e-labInnovations/CampusCast/main/src/WiFiManager/wm_strings_en.h

/**
 * wm_strings_en.h
 * engligh strings for
 * WiFiManager, a library for the ESP8266/Arduino platform
 * for configuration of WiFi credentials using a Captive Portal
 *
 * @author Creator tzapu
 * @author tablatronix
 * @version 0.0.0
 * @license MIT
 */

#ifndef _WM_STRINGS_EN_H_
#define _WM_STRINGS_EN_H_


#ifndef WIFI_MANAGER_OVERRIDE_STRINGS
// !!! ABOVE WILL NOT WORK if you define in your sketch, must be build flag, if anyone one knows how to order includes to be able to do this it would be neat.. I have seen it done..

// strings files must include a consts file!
#include "wm_consts_en.h" // include constants, tokens, routes

const char WM_LANGUAGE[] PROGMEM = "en-US"; // i18n lang code

const char HTTP_HEAD_START[]       PROGMEM = "<!DOCTYPE html>"
"<html lang='en'><head>"
"<meta name='format-detection' content='telephone=no'>"
"<meta charset='UTF-8'>"
"<meta  name='viewport' content='width=device-width,initial-scale=1,user-scalable=no'/>"
"<title>{v}</title>";

const char HTTP_SCRIPT[]           PROGMEM = "<script>function c(l){"
"document.getElementById('s').value=l.getAttribute('data-ssid')||l.innerText||l.textContent;"
"p = l.nextElementSibling.classList.contains('l');"
"document.getElementById('p').disabled = !p;"
"if(p)document.getElementById('p').focus();};"
"function f() {var x = document.getElementById('p');x.type==='password'?x.type='text':x.type='password';}"
"</script>"; // @todo add button states, disable on click , show ack , spinner etc

const char HTTP_HEAD_END[]         PROGMEM = "</head><body class='{c}'><div class='wrap'>"; // {c} = _bodyclass
// example of embedded logo, base64 encoded inline, No styling here
const char HTTP_ROOT_MAIN[]        PROGMEM = "<svg id=\"OBJECTS\" xmlns=\"http://www.w3.org/2000/svg\" viewBox=\"0 0 600 100\"><defs><style>.cls-3{fill:#3cb371}</style></defs><text transform=\"translate(32.22 76.61)\" style=\"font-size:81px\"><tspan x=\"0\" y=\"0\" style=\"font-family:MontserratAlternates-Bold,'Montserrat Alternates';font-weight:700;letter-spacing:-.02em;fill:#2b2f60\">C</tspan><tspan x=\"57.83\" y=\"0\" style=\"font-family:MontserratAlternates-Bold,'Montserrat Alternates';font-weight:700;fill:#2b2f60\">ampus</tspan><tspan x=\"353.24\" y=\"0\" style=\"letter-spacing:-.02em;fill:#3cb371;font-family:MontserratAlternates-Regular,'Montserrat Alternates'\">C</tspan><tspan x=\"409.61\" y=\"0\" style=\"fill:#3cb371;font-family:MontserratAlternates-Regular,'Montserrat Alternates'\">ast</tspan></text><path d=\"m42.29 60.68-6.91 17.67c-1.11 2.84 1.86 5.56 4.59 4.2l19.38-9.64-17.06-12.23Z\" style=\"fill:#2b2f60\"/><rect class=\"cls-3\" x=\"438.47\" y=\"11.64\" width=\"15.39\" height=\"3.88\" rx=\"1.94\" ry=\"1.94\" transform=\"rotate(-49.2 446.163 13.581)\"/><rect class=\"cls-3\" x=\"423.93\" y=\"7.52\" width=\"15.39\" height=\"3.88\" rx=\"1.94\" ry=\"1.94\" transform=\"rotate(-99.2 431.624 9.465)\"/><rect class=\"cls-3\" x=\"444.66\" y=\"25.41\" width=\"15.39\" height=\"3.88\" rx=\"1.94\" ry=\"1.94\" transform=\"rotate(.8 452.844 27.636)\"/></svg><h3>{v}</h3>";
// const char HTTP_ROOT_MAIN[]        PROGMEM = "<h1>{t}</h1><h3>{v}</h3>";

const char * const HTTP_PORTAL_MENU[] PROGMEM = {
"<form action='/wifi'    method='get'><button>Configure WiFi</button></form><br/>\n", // MENU_WIFI
"<form action='/0wifi'   method='get'><button>Configure WiFi (No Scan)</button></form><br/>\n", // MENU_WIFINOSCAN
"<form action='/info'    method='get'><button>Info</button></form><br/>\n", // MENU_INFO
"<form action='/param'   method='get'><button>Setup</button></form><br/>\n",//MENU_PARAM
"<form action='/close'   method='get'><button>Close</button></form><br/>\n", // MENU_CLOSE
"<form action='/restart' method='get'><button>Restart</button></form><br/>\n",// MENU_RESTART
"<form action='/exit'    method='get'><button>Exit</button></form><br/>\n",  // MENU_EXIT
"<form action='/erase'   method='get'><button class='D'>Erase</button></form><br/>\n", // MENU_ERASE
"<form action='/update'  method='get'><button>Update</button></form><br/>\n",// MENU_UPDATE
"<hr><br/>" // MENU_SEP
};

// const char HTTP_PORTAL_OPTIONS[]   PROGMEM = strcat(HTTP_PORTAL_MENU[0] , HTTP_PORTAL_MENU[3] , HTTP_PORTAL_MENU[7]);
const char HTTP_PORTAL_OPTIONS[]   PROGMEM = "";
const char HTTP_ITEM_QI[]          PROGMEM = "<div role='img' aria-label='{r}%' title='{r}%' class='q q-{q} {i} {h}'></div>"; // rssi icons
const char HTTP_ITEM_QP[]          PROGMEM = "<div class='q {h}'>{r}%</div>"; // rssi percentage {h} = hidden showperc pref
const char HTTP_ITEM[]             PROGMEM = "<div><a href='#p' onclick='c(this)' data-ssid='{V}'>{v}</a>{qi}{qp}</div>"; // {q} = HTTP_ITEM_QI, {r} = HTTP_ITEM_QP
// const char HTTP_ITEM[]            PROGMEM = "<div><a href='#p' onclick='c(this)'>{v}</a> {R} {r}% {q} {e}</div>"; // test all tokens

const char HTTP_FORM_START[]       PROGMEM = "<form method='POST' action='{v}'>";
const char HTTP_FORM_WIFI[]        PROGMEM = "<label for='s'>SSID</label><input id='s' name='s' maxlength='32' autocorrect='off' autocapitalize='none' placeholder='{v}'><br/><label for='p'>Password</label><input id='p' name='p' maxlength='64' type='password' placeholder='{p}'><input type='checkbox' onclick='f()'> Show Password";
const char HTTP_FORM_WIFI_END[]    PROGMEM = "";
const char HTTP_FORM_STATIC_HEAD[] PROGMEM = "<hr><br/>";
const char HTTP_FORM_END[]         PROGMEM = "<br/><br/><button type='submit'>Save</button></form>";
const char HTTP_FORM_LABEL[]       PROGMEM = "<label for='{i}'>{t}</label>";
const char HTTP_FORM_PARAM_HEAD[]  PROGMEM = "<hr><br/>";
const char HTTP_FORM_PARAM[]       PROGMEM = "<br/><input id='{i}' name='{n}' maxlength='{l}' value='{v}' {c}>\n"; // do not remove newline!

const char HTTP_SCAN_LINK[]        PROGMEM = "<br/><form action='/wifi?refresh=1' method='POST'><button name='refresh' value='1'>Refresh</button></form>";
const char HTTP_SAVED[]            PROGMEM = "<div class='msg'>Saving Credentials<br/>Trying to connect ESP to network.<br />If it fails reconnect to AP to try again</div>";
const char HTTP_PARAMSAVED[]       PROGMEM = "<div class='msg S'>Saved<br/></div>";
const char HTTP_END[]              PROGMEM = "</div></body></html>";
const char HTTP_ERASEBTN[]         PROGMEM = "<br/><form action='/erase' method='get'><button class='D'>Erase WiFi Config</button></form>";
const char HTTP_UPDATEBTN[]        PROGMEM = "<br/><form action='/update' method='get'><button>Update</button></form>";
const char HTTP_BACKBTN[]          PROGMEM = "<hr><br/><form action='/' method='get'><button>Back</button></form>";

const char HTTP_STATUS_ON[]        PROGMEM = "<div class='msg S'><strong>Connected</strong> to {v}<br/><em><small>with IP {i}</small></em></div>";
const char HTTP_STATUS_OFF[]       PROGMEM = "<div class='msg {c}'><strong>Not Connected</strong> to {v}{r}</div>"; // {c=class} {v=ssid} {r=status_off}
const char HTTP_STATUS_OFFPW[]     PROGMEM = "<br/>Authentication Failure"; // STATION_WRONG_PASSWORD,  no eps32
const char HTTP_STATUS_OFFNOAP[]   PROGMEM = "<br/>AP not found";   // WL_NO_SSID_AVAIL
const char HTTP_STATUS_OFFFAIL[]   PROGMEM = "<br/>Could not Connect"; // WL_CONNECT_FAILED
const char HTTP_STATUS_NONE[]      PROGMEM = "<div class='msg'>No AP set</div>";
const char HTTP_BR[]               PROGMEM = "<br/>";

const char HTTP_STYLE[]            PROGMEM = "<style>"
".c,body{text-align:center;font-family:verdana}div,input,select{padding:5px;font-size:1em;margin:5px 0;box-sizing:border-box}"
"input,button,select,.msg{border-radius:.3rem;width: 100%}input[type=radio],input[type=checkbox]{width:auto}"
"button,input[type='button'],input[type='submit']{cursor:pointer;border:0;background-color:#1fa3ec;color:#fff;line-height:2.4rem;font-size:1.2rem;width:100%}"
"input[type='file']{border:1px solid #1fa3ec}"
".wrap {text-align:left;display:inline-block;min-width:260px;max-width:500px}"
// links
"a{color:#000;font-weight:700;text-decoration:none}a:hover{color:#1fa3ec;text-decoration:underline}"
// quality icons
".q{height:16px;margin:0;padding:0 5px;text-align:right;min-width:38px;float:right}.q.q-0:after{background-position-x:0}.q.q-1:after{background-position-x:-16px}.q.q-2:after{background-position-x:-32px}.q.q-3:after{background-position-x:-48px}.q.q-4:after{background-position-x:-64px}.q.l:before{background-position-x:-80px;padding-right:5px}.ql .q{float:left}.q:after,.q:before{content:'';width:16px;height:16px;display:inline-block;background-repeat:no-repeat;background-position: 16px 0;"
"background-image:url('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');}"
// icons @2x media query (32px rescaled)
"@media (-webkit-min-device-pixel-ratio: 2),(min-resolution: 192dpi){.q:before,.q:after {"
"background-image:url('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');"
"background-size: 95px 16px;}}"
// msg callouts
".msg{padding:20px;margin:20px 0;border:1px solid #eee;border-left-width:5px;border-left-color:#777}.msg h4{margin-top:0;margin-bottom:5px}.msg.P{border-left-color:#1fa3ec}.msg.P h4{color:#1fa3ec}.msg.D{border-left-color:#dc3630}.msg.D h4{color:#dc3630}.msg.S{border-left-color: #5cb85c}.msg.S h4{color: #5cb85c}"
// lists
"dt{font-weight:bold}dd{margin:0;padding:0 0 0.5em 0;min-height:12px}"
"td{vertical-align: top;}"
".h{display:none}"
"button{transition: 0s opacity;transition-delay: 3s;transition-duration: 0s;cursor: pointer}"
"button.D{background-color:#dc3630}"
"button:active{opacity:50% !important;cursor:wait;transition-delay: 0s}"
// invert
"body.invert,body.invert a,body.invert h1 {background-color:#060606;color:#fff;}"
"body.invert .msg{color:#fff;background-color:#282828;border-top:1px solid #555;border-right:1px solid #555;border-bottom:1px solid #555;}"
"body.invert .q[role=img]{-webkit-filter:invert(1);filter:invert(1);}"
":disabled {opacity: 0.5;}"
"</style>";

#ifndef WM_NOHELP
const char HTTP_HELP[]             PROGMEM =
 "<br/><h3>Available Pages</h3><hr>"
 "<table class='table'>"
 "<thead><tr><th>Page</th><th>Function</th></tr></thead><tbody>"
 "<tr><td><a href='/'>/</a></td>"
 "<td>Menu page.</td></tr>"
 "<tr><td><a href='/wifi'>/wifi</a></td>"
 "<td>Show WiFi scan results and enter WiFi configuration.(/0wifi noscan)</td></tr>"
 "<tr><td><a href='/wifisave'>/wifisave</a></td>"
 "<td>Save WiFi configuration information and configure device. Needs variables supplied.</td></tr>"
 "<tr><td><a href='/param'>/param</a></td>"
 "<td>Parameter page</td></tr>"
 "<tr><td><a href='/info'>/info</a></td>"
 "<td>Information page</td></tr>"
 "<tr><td><a href='/u'>/u</a></td>"
 "<td>OTA Update</td></tr>"
 "<tr><td><a href='/close'>/close</a></td>"
 "<td>Close the captiveportal popup,configportal will remain active</td></tr>"
 "<tr><td>/exit</td>"
 "<td>Exit Config Portal, configportal will close</td></tr>"
 "<tr><td>/restart</td>"
 "<td>Reboot the device</td></tr>"
 "<tr><td>/erase</td>"
 "<td>Erase WiFi configuration and reboot Device. Device will not reconnect to a network until new WiFi configuration data is entered.</td></tr>"
 "</table>";
#else
const char HTTP_HELP[]             PROGMEM = "";
#endif

const char HTTP_UPDATE[] PROGMEM = "Upload New Firmware<br/><form method='POST' action='u' enctype='multipart/form-data' onchange=\"(function(el){document.getElementById('uploadbin').style.display = el.value=='' ? 'none' : 'initial';})(this)\"><input type='file' name='update' accept='.bin,application/octet-stream'><button id='uploadbin' type='submit' class='h D'>Update</button></form><small><a href='http://192.168.4.1/update' target='_blank'>* May not function inside captive portal, Open in browser http://192.168.4.1</a><small>";
const char HTTP_UPDATE_FAIL[] PROGMEM = "<div class='msg D'><strong>Update Failed!</strong><Br/>Reboot device and try again</div>";
const char HTTP_UPDATE_SUCCESS[] PROGMEM = "<div class='msg S'><strong>Update Successful.  </strong> <br/> Device Rebooting now...</div>";

#ifdef WM_JSTEST
const char HTTP_JS[] PROGMEM =
"<script>function postAjax(url, data, success) {"
"    var params = typeof data == 'string' ? data : Object.keys(data).map("
"            function(k){ return encodeURIComponent(k) + '=' + encodeURIComponent(data[k]) }"
"        ).join('&');"
"    var xhr = window.XMLHttpRequest ? new XMLHttpRequest() : new ActiveXObject(\"Microsoft.XMLHTTP\");"
"    xhr.open('POST', url);"
"    xhr.onreadystatechange = function() {"
"        if (xhr.readyState>3 && xhr.status==200) { success(xhr.responseText); }"
"    };"
"    xhr.setRequestHeader('X-Requested-With', 'XMLHttpRequest');"
"    xhr.setRequestHeader('Content-Type', 'application/x-www-form-urlencoded');"
"    xhr.send(params);"
"    return xhr;}"
"postAjax('/status', 'p1=1&p2=Hello+World', function(data){ console.log(data); });"
"postAjax('/status', { p1: 1, p2: 'Hello World' }, function(data){ console.log(data); });"
"</script>";
#endif

// Info html
// @todo remove html elements from progmem, repetetive strings
#ifdef ESP32
	const char HTTP_INFO_esphead[]    PROGMEM = "<h3>esp32</h3><hr><dl>";
	const char HTTP_INFO_chiprev[]    PROGMEM = "<dt>Chip Rev</dt><dd>{1}</dd>";
  	const char HTTP_INFO_lastreset[]  PROGMEM = "<dt>Last reset reason</dt><dd>CPU0: {1}<br/>CPU1: {2}</dd>";
  	const char HTTP_INFO_aphost[]     PROGMEM = "<dt>Access Point Hostname</dt><dd>{1}</dd>";
    const char HTTP_INFO_psrsize[]    PROGMEM = "<dt>PSRAM Size</dt><dd>{1} bytes</dd>";
	const char HTTP_INFO_temp[]       PROGMEM = "<dt>Temperature</dt><dd>{1} C&deg; / {2} F&deg;</dd><dt>Hall</dt><dd>{3}</dd>";
#else
	const char HTTP_INFO_esphead[]    PROGMEM = "<h3>esp8266</h3><hr><dl>";
	const char HTTP_INFO_fchipid[]    PROGMEM = "<dt>Flash Chip ID</dt><dd>{1}</dd>";
	const char HTTP_INFO_corever[]    PROGMEM = "<dt>Core Version</dt><dd>{1}</dd>";
	const char HTTP_INFO_bootver[]    PROGMEM = "<dt>Boot Version</dt><dd>{1}</dd>";
	const char HTTP_INFO_lastreset[]  PROGMEM = "<dt>Last reset reason</dt><dd>{1}</dd>";
	const char HTTP_INFO_flashsize[]  PROGMEM = "<dt>Real Flash Size</dt><dd>{1} bytes</dd>";
#endif

const char HTTP_INFO_memsmeter[]  PROGMEM = "<br/><progress value='{1}' max='{2}'></progress></dd>";
const char HTTP_INFO_memsketch[]  PROGMEM = "<dt>Memory - Sketch Size</dt><dd>Used / Total bytes<br/>{1} / {2}";
const char HTTP_INFO_freeheap[]   PROGMEM = "<dt>Memory - Free Heap</dt><dd>{1} bytes available</dd>";
const char HTTP_INFO_wifihead[]   PROGMEM = "<br/><h3>WiFi</h3><hr>";
const char HTTP_INFO_uptime[]     PROGMEM = "<dt>Uptime</dt><dd>{1} Mins {2} Secs</dd>";
const char HTTP_INFO_chipid[]     PROGMEM = "<dt>Chip ID</dt><dd>{1}</dd>";
const char HTTP_INFO_idesize[]    PROGMEM = "<dt>Flash Size</dt><dd>{1} bytes</dd>";
const char HTTP_INFO_sdkver[]     PROGMEM = "<dt>SDK Version</dt><dd>{1}</dd>";
const char HTTP_INFO_cpufreq[]    PROGMEM = "<dt>CPU Frequency</dt><dd>{1}MHz</dd>";
const char HTTP_INFO_apip[]       PROGMEM = "<dt>Access Point IP</dt><dd>{1}</dd>";
const char HTTP_INFO_apmac[]      PROGMEM = "<dt>Access Point MAC</dt><dd>{1}</dd>";
const char HTTP_INFO_apssid[]     PROGMEM = "<dt>Access Point SSID</dt><dd>{1}</dd>";
const char HTTP_INFO_apbssid[]    PROGMEM = "<dt>BSSID</dt><dd>{1}</dd>";
const char HTTP_INFO_stassid[]    PROGMEM = "<dt>Station SSID</dt><dd>{1}</dd>";
const char HTTP_INFO_staip[]      PROGMEM = "<dt>Station IP</dt><dd>{1}</dd>";
const char HTTP_INFO_stagw[]      PROGMEM = "<dt>Station Gateway</dt><dd>{1}</dd>";
const char HTTP_INFO_stasub[]     PROGMEM = "<dt>Station Subnet</dt><dd>{1}</dd>";
const char HTTP_INFO_dnss[]       PROGMEM = "<dt>DNS Server</dt><dd>{1}</dd>";
const char HTTP_INFO_host[]       PROGMEM = "<dt>Hostname</dt><dd>{1}</dd>";
const char HTTP_INFO_stamac[]     PROGMEM = "<dt>Station MAC</dt><dd>{1}</dd>";
const char HTTP_INFO_conx[]       PROGMEM = "<dt>Connected</dt><dd>{1}</dd>";
const char HTTP_INFO_autoconx[]   PROGMEM = "<dt>Autoconnect</dt><dd>{1}</dd>";

const char HTTP_INFO_aboutver[]     PROGMEM = "<dt>WiFiManager</dt><dd>{1}</dd>";
const char HTTP_INFO_aboutarduino[] PROGMEM = "<dt>Arduino</dt><dd>{1}</dd>";
const char HTTP_INFO_aboutsdk[]     PROGMEM = "<dt>ESP-SDK/IDF</dt><dd>{1}</dd>";
const char HTTP_INFO_aboutdate[]    PROGMEM = "<dt>Build Date</dt><dd>{1}</dd>";

const char S_brand[]              PROGMEM = "CampusCast";
const char S_debugPrefix[]        PROGMEM = "*wm:";
const char S_y[]                  PROGMEM = "Yes";
const char S_n[]                  PROGMEM = "No";
const char S_enable[]             PROGMEM = "Enabled";
const char S_disable[]            PROGMEM = "Disabled";
const char S_GET[]                PROGMEM = "GET";
const char S_POST[]               PROGMEM = "POST";
const char S_NA[]                 PROGMEM = "Unknown";
const char S_passph[]             PROGMEM = "********";
const char S_titlewifisaved[]     PROGMEM = "Credentials Saved";
const char S_titlewifisettings[]  PROGMEM = "Settings Saved";
const char S_titlewifi[]          PROGMEM = "Config ESP";
const char S_titleinfo[]          PROGMEM = "Info";
const char S_titleparam[]         PROGMEM = "Setup";
const char S_titleparamsaved[]    PROGMEM = "Setup Saved";
const char S_titleexit[]          PROGMEM = "Exit";
const char S_titlereset[]         PROGMEM = "Reset";
const char S_titleerase[]         PROGMEM = "Erase";
const char S_titleclose[]         PROGMEM = "Close";
const char S_options[]            PROGMEM = "options";
const char S_nonetworks[]         PROGMEM = "No networks found. Refresh to scan again.";
const char S_staticip[]           PROGMEM = "Static IP";
const char S_staticgw[]           PROGMEM = "Static Gateway";
const char S_staticdns[]          PROGMEM = "Static DNS";
const char S_subnet[]             PROGMEM = "Subnet";
const char S_exiting[]            PROGMEM = "Exiting";
const char S_resetting[]          PROGMEM = "Module will reset in a few seconds.";
const char S_closing[]            PROGMEM = "You can close the page, portal will continue to run";
const char S_error[]              PROGMEM = "An Error Occured";
const char S_notfound[]           PROGMEM = "File Not Found\n\n";
const char S_uri[]                PROGMEM = "URI: ";
const char S_method[]             PROGMEM = "\nMethod: ";
const char S_args[]               PROGMEM = "\nArguments: ";
const char S_parampre[]           PROGMEM = "param_";

// debug strings
const char D_HR[]                 PROGMEM = "--------------------";


// softap ssid default prefix
#ifdef ESP8266
    const char S_ssidpre[]        PROGMEM = "ESP";
#elif defined(ESP32)
    const char S_ssidpre[]        PROGMEM = "ESP32";
#else
    const char S_ssidpre[]        PROGMEM = "WM";
#endif

// END WIFI_MANAGER_OVERRIDE_STRINGS
#endif

#endif
